MaverickUK/HDDSynth/2_prototype_mk5/software/beep.py

import time
import math
import array
import synthio

import rgb_led
import settings
from beep_profiles import (
    PROFILE,
    PITCH_MEDIUM,
    LENGTH_SHORT,
    WAVE_SIN,
    WAVE_TRIANGLE,
    CATEGORY_ERROR,
    CATEGORY_OPERATION,
)

# Buffer after each note so the envelope release finishes before the next gap.
# Shared so a replayed LED-only pattern can reproduce the same cadence.
RELEASE_BUFFER_S = 0.05


def _category_colour(category):
    """Status LED colour that flashes alongside this category of beep."""
    if category == CATEGORY_ERROR:
        return settings.RGB_LED_ERROR_COLOUR
    if category == CATEGORY_OPERATION:
        return settings.RGB_LED_OPERATION_COLOUR
    return None

# --- Internal Helpers ---

# Lookup tables are identical for every beep of a given wave type, so cache
# them the first time they're generated instead of recomputing on every beep.
_waveform_cache = {}


def _build_waveform(wave_type):
    """Generates a 512-sample lookup table for the synthesizer."""
    size = 512

    if wave_type == WAVE_SIN:
        return array.array('h', [
            int(math.sin(2 * math.pi * i / size) * 32767)
            for i in range(size)
        ])

    if wave_type == WAVE_TRIANGLE:
        samples = array.array('h', [0] * size)
        for i in range(size):
            if i < size // 2:
                samples[i] = int(-32767 + (i * 65535 / (size // 2)))
            else:
                samples[i] = int(32767 - ((i - size // 2) * 65535 / (size // 2)))
        return samples

    return _build_waveform(WAVE_SIN)


def _get_waveform(wave_type=WAVE_SIN):
    """Returns the cached lookup table for wave_type, building it on first use."""
    if wave_type not in _waveform_cache:
        _waveform_cache[wave_type] = _build_waveform(wave_type)
    return _waveform_cache[wave_type]


def _get_envelope():
    """Returns a standard ADSR envelope to prevent clicking."""
    return synthio.Envelope(
        attack_time=0.02,
        decay_time=0.1,
        sustain_level=0.8,
        release_time=0.05,
    )

# --- Public API ---

def play_beep(mixer, pitch=PITCH_MEDIUM, count=1, length=LENGTH_SHORT, volume=0.8,
              wave=WAVE_SIN, led_colour=None):
    """Plays a smooth beep tone on the dedicated beep voice.

    If led_colour is given, the RGB status LED flashes in time with the beeps.
    """
    waveform = _get_waveform(wave)
    envelope = _get_envelope()
    synth = synthio.Synthesizer(sample_rate=mixer.sample_rate)

    # Use the dedicated beep voice so the idle/access loops keep playing underneath.
    beep_voice = mixer.voice[settings.MIXER_VOICES]
    beep_voice.play(synth)
    beep_voice.level = volume

    for i in range(count):
        note = synthio.Note(frequency=pitch, waveform=waveform, envelope=envelope)

        if led_colour:
            rgb_led.set_rgb(*led_colour)

        synth.press(note)
        time.sleep(length)
        synth.release(note)

        if led_colour:
            rgb_led.off()

        # Small buffer for the envelope release to finish
        time.sleep(RELEASE_BUFFER_S)

        # Inter-beep gap
        if i < count - 1:
            time.sleep(length * 0.4)

    beep_voice.stop()
    synth.deinit()

    if led_colour:
        rgb_led.invalidate_activity()


def play_beep_type(mixer, beep_type):
    """Looks up a beep profile by name and plays it."""
    config = PROFILE.get(beep_type.upper())

    if config is None:
        print(f"Warning: Beep type '{beep_type}' not found in beep.py")
        return

    play_beep(
        mixer,
        pitch=config.get("pitch", PITCH_MEDIUM),
        count=config.get("count", 1),
        length=config.get("length", LENGTH_SHORT),
        wave=config.get("wave", WAVE_SIN),
        led_colour=_category_colour(config.get("category")),
    )
